winnand/winnand-tkl-board/Images/Final Render.PNG

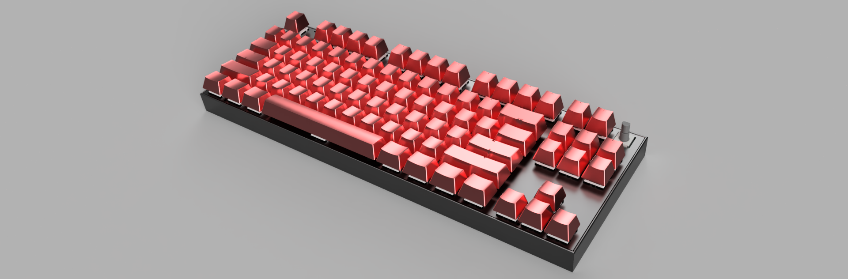
Images/Final Render.PNG
