winnand/winnand-tkl-board/Images/Full CAD.png

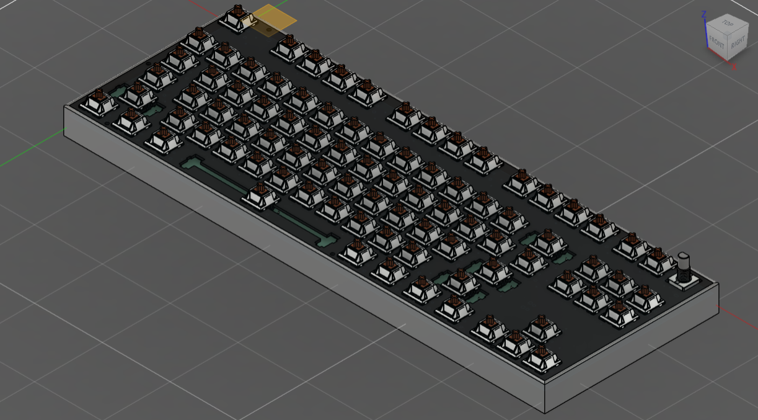
Images/Full CAD.png
