winnand/winnand-tkl-board/Images/KB Plate Underside.png

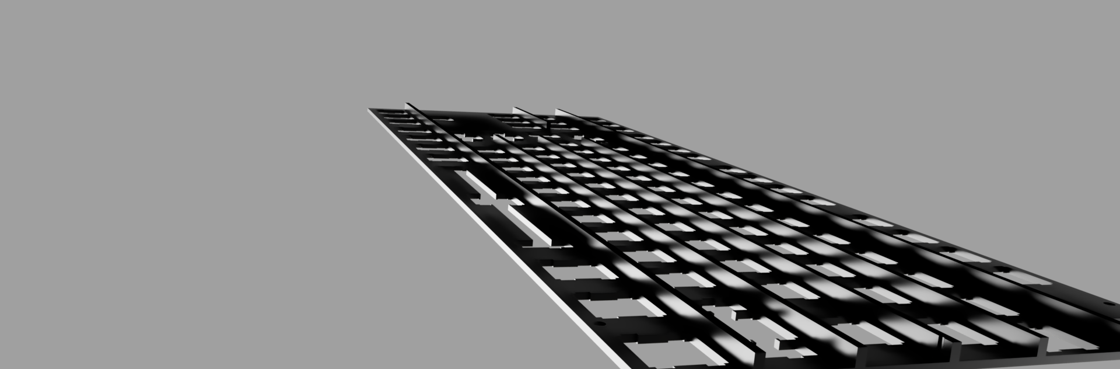
Images/KB Plate Underside.png
